JShull/Turbine_Challenge/Media/MK4Layout_10-10_2024.png

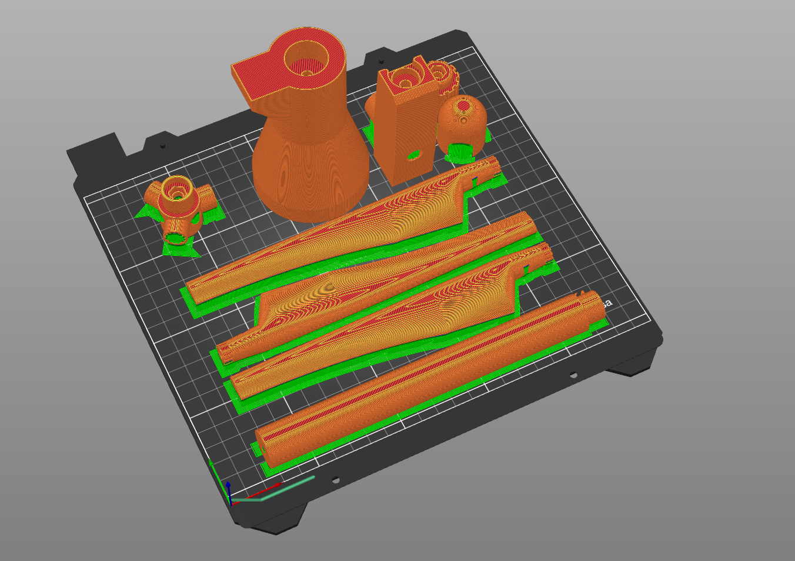
Media/MK4Layout_10-10_2024.png
