JShull/Turbine_Challenge/Media/TurbineBack.jpg

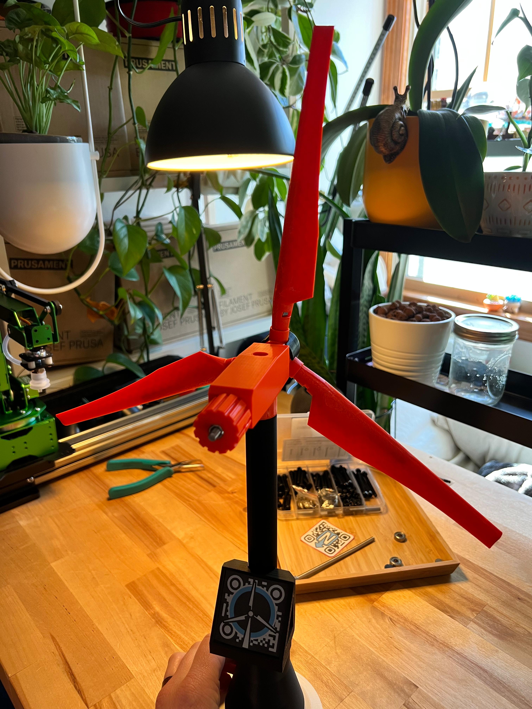
Media/TurbineBack.jpg
