JShull/Turbine_Challenge/Media/TurbineSide.jpg

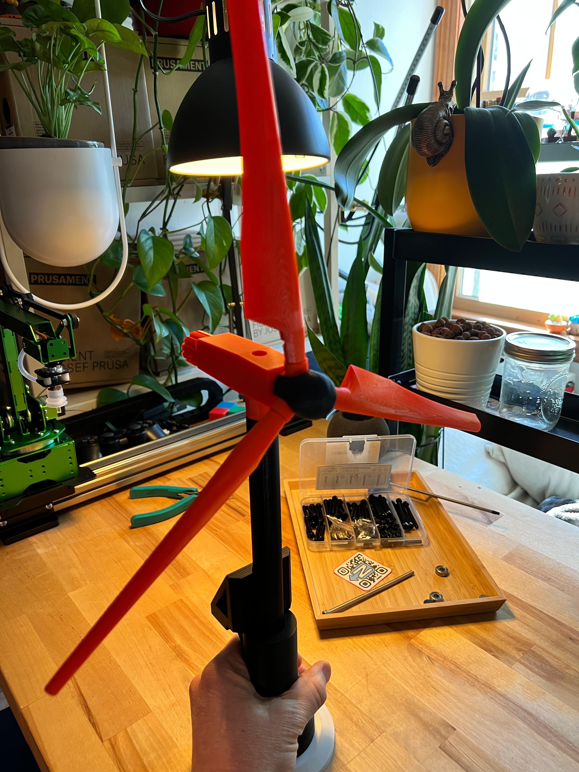
Media/TurbineSide.jpg
