JShull/Turbine_Challenge/Media/FusionParts2.png

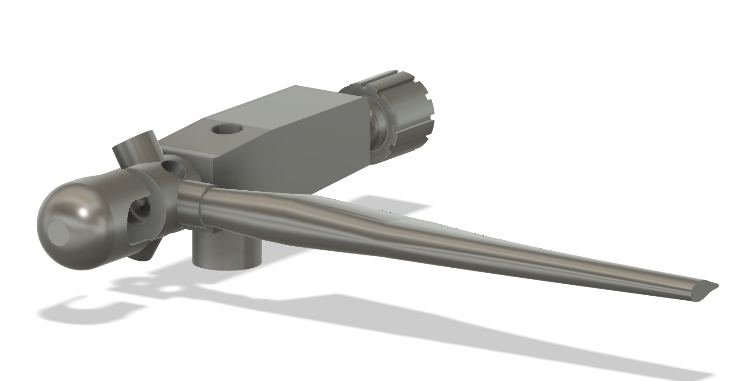
Media/FusionParts2.png
