JShull/Turbine_Challenge/Media/FusionParts.png

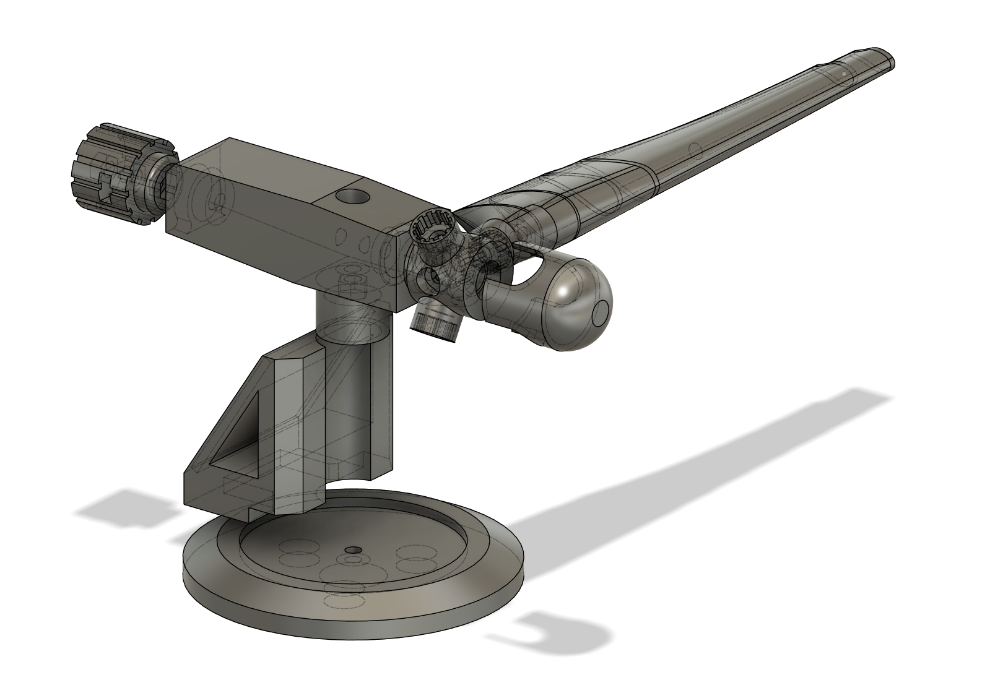
Media/FusionParts.png
