JShull/Turbine_Challenge/Media/BladeAssembly.png

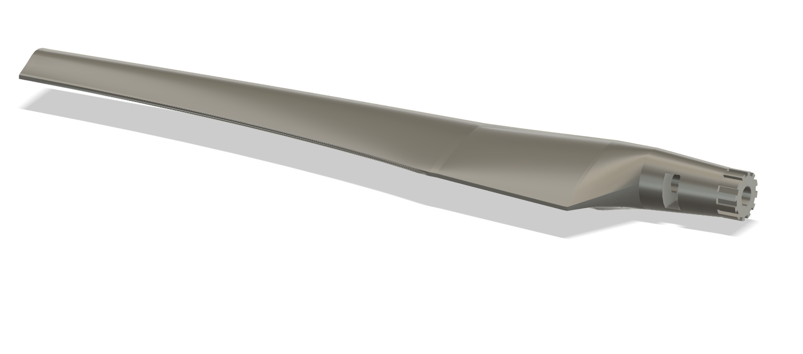
Media/BladeAssembly.png
