JShull/Turbine_Challenge/Media/HousingAssembly.png

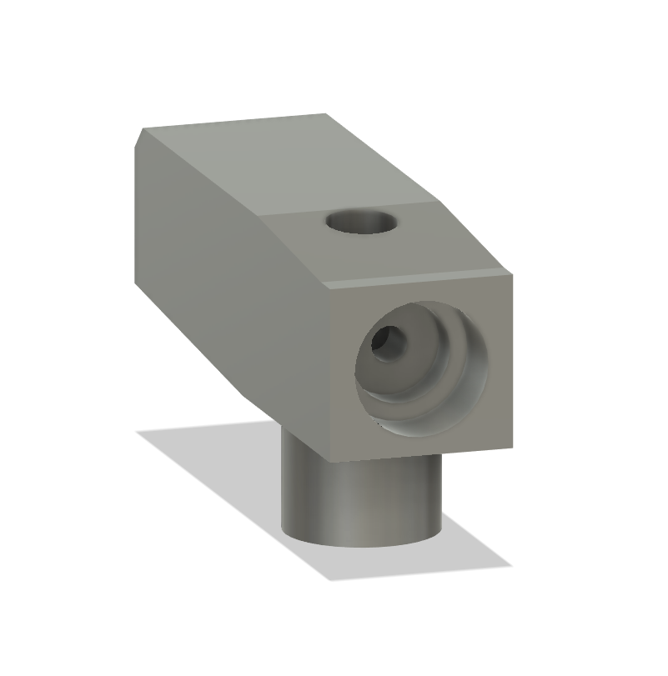
Media/HousingAssembly.png
