JShull/Turbine_Challenge/Media/NoseAssembly.png

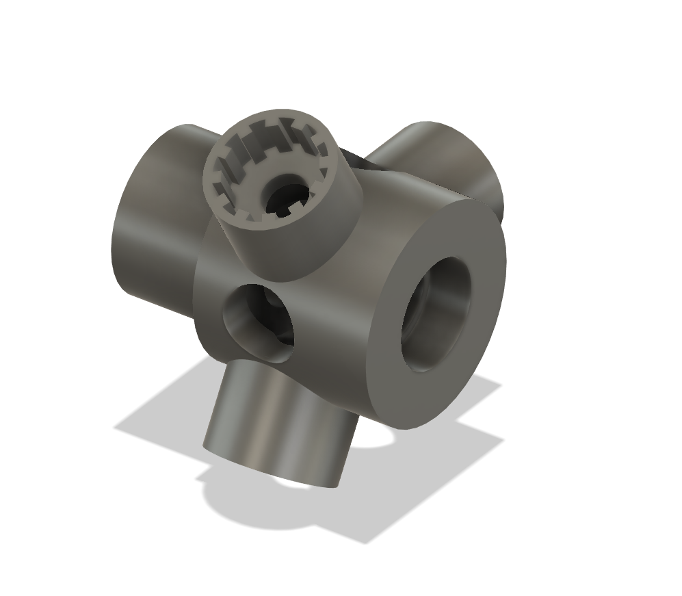
Media/NoseAssembly.png
